ezcGman/n64-denc-nus-adapter/castellated/N64-DENC-NUS-Adapter-Castellated.kicad_sch

## KiCad design castellated/N64-DENC-NUS-Adapter-Castellated.kicad_sch (2023-02-28)

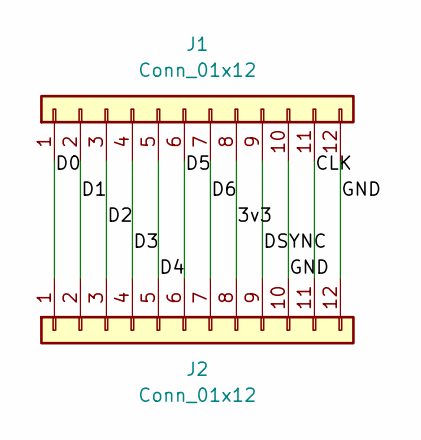
[picture p6: schematic N64-DENC-NUS-Adapter-Castellated.kicad_sch]

Parts:
J1: Conn_01x12; EdgeConnector_1x12_P1.27mm_Castellated
J2: Conn_01x12; PinHeader_1x12_P2.00mm_Vertical_SMD_Pin1Left

Connections:
3v3: J1.8, J2.8
CLK: J1.11, J2.11
D0: J1.1, J2.1
D1: J1.2, J2.2
D2: J1.3, J2.3
D3: J1.4, J2.4
D4: J1.5, J2.5
D5: J1.6, J2.6
D6: J1.7, J2.7
DSYNC: J1.9, J2.9
GND: J1.10, J1.12, J2.10, J2.12
